cadus/incinerator/src/incinerator/incinerator.cpp

/*
 * SPDX-License-Identifier: GPL-3.0-or-later
 * This file is part of CADUS Incinerator, https://github.com/cadus/incinerator
 * Copyright (C) 2019-2020 Patrick Huesmann <info@patrick-huesmann.de>
 *
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
 * You should have received a copy of the GNU General Public License
 * along with this program.  If not, see <https://www.gnu.org/licenses/>.
 */

#include "incinerator.h"

#include <map>

#include "hw_config.h"
#include "util/sys_config.h"
#include "util/syslog.h"
#include "ui/screens/screen.h"

Incinerator::Incinerator()
: burnerMain("MAIN", IGNITION_MAIN, TEMP_MAIN_CS, VALVE_MAIN)
, burnerAft("AFT", IGNITION_AFT, TEMP_AFT_CS, VALVE_AFT)
, airPump(AIRPMP, PWM_CH_AIRPMP)
{
}

void Incinerator::init()
{
    burnerMain.init();
    burnerAft.init();
    airPump.init();
    reset();
}

void Incinerator::task()
{
    burnerMain.task();
    burnerAft.task();
    fsm();
}

Incinerator::mode Incinerator::getMode() const
{
    return _mode;
}

bool Incinerator::isCoolingDown() const
{
    return _mode == mode::coolDown
           || _mode == mode::abortCoolDown
           || _mode == mode::failureCoolDown;
}

bool Incinerator::isFinished() const
{
    return _mode == mode::finished
           || _mode == mode::aborted
           || _mode == mode::failed;
}

std::string Incinerator::getModeStr() const
{
    static const std::map<mode, std::string> lookupTbl {
        {idle, "Idle"},
        {startAft, "StartAft"},
        {waitAft, "WaitAft"},
        {startMain, "StartMain"},
        {waitMain, "WaitMain"},
        {burnActive, "BurnActive"},
        {coolDown, "CoolDown"},
        {finished, "Finished"},
        {failed, "Failed"}
    };
    auto it = lookupTbl.find(getMode());
    return it != lookupTbl.end() ? it->second : "N/A";
}

void Incinerator::start()
{
    _startFlag = true;
}

void Incinerator::abort()
{
    _abortFlag = true;
}

void Incinerator::reset()
{
    doReset();
    _mode = mode::idle;
}

void Incinerator::doReset()
{
    Screen::setProgress(0);
    burnerMain.reset();
    burnerAft.reset();
    airPump.off();
}

void Incinerator::doFail()
{
    doReset();
    _mode = mode::failureCoolDown;
}

void Incinerator::doAbort()
{
    syslog(LOG_INFO, "Burn process aborted by user");
    doReset();
    _mode = mode::abortCoolDown;
}

std::string Incinerator::fmt_minutes(uint32_t seconds) const
{
    char tmp[100];
    snprintf(tmp, sizeof(tmp), "%d:%02d", seconds / 60, seconds % 60);
    return std::string(tmp);
}


void Incinerator::fsm()
{
    float percent, temp;
    switch (_mode) {
    default:
    case mode::idle:
        if (!_startFlag) {
            break;
        }
        _startFlag = false;
        _abortFlag = false;
        _tempMax = nanf("");
        _mode = mode::startAft;
        // fall through
    case mode::startAft:
        syslog(LOG_INFO, "Starting afterburner");
        burnerAft.start();
        _mode = mode::waitAft;
        break;
    case mode::waitAft:
        if (_abortFlag) {
            doAbort();
            break;
        }
        if (burnerAft.getMode() == BurnChamber::mode::failed) {
            syslog(LOG_INFO, "Afterburner failed");
            doFail();
            break;
        }
        if (!burnerAft.isBurning()) {
            break;
        }
        _mode = mode::startMain;
        // fall through
    case mode::startMain:
        syslog(LOG_INFO, "Starting main burner");
        burnerMain.start();
        airPump.on();
        _mode = mode::waitMain;
        // fall through
    case mode::waitMain:
        if (_abortFlag) {
            doAbort();
            break;
        }
        if (burnerMain.getMode() == BurnChamber::mode::failed
            || burnerAft.getMode() == BurnChamber::mode::failed) {
            syslog(LOG_INFO, "Burner failed");
            doFail();
            break;
        }
        if (!burnerMain.isBurning()) {
            break;
        }
        _mode = mode::burnActive;
        _burn_seconds = sysconfig.get("burn_time") * 60;
        _burn_seconds_elapsed = 0;
        syslog(LOG_INFO, "Burning in progress");
        _timeout.set(1000);
        // fall through
    case mode::burnActive:
        if (_abortFlag) {
            doAbort();
            break;
        }
        if (burnerMain.getMode() == BurnChamber::mode::failed
            || burnerAft.getMode() == BurnChamber::mode::failed) {
            syslog(LOG_INFO, "Burner failed");
            doFail();
            break;
        }
        if (!_timeout.elapsed()) {
            break;
        }
        _burn_seconds_elapsed++;
        _timeout.set(1000);
        percent = (100.f * (float)_burn_seconds_elapsed) / (float)_burn_seconds;
        syslog(LOG_INFO, "Burning %s / %s (%d%%)",
                         fmt_minutes(_burn_seconds_elapsed).c_str(),
                         fmt_minutes(_burn_seconds).c_str(),
                         (int)percent);
        Screen::setProgress(percent);
        if (_burn_seconds_elapsed < _burn_seconds) {
            break;
        }
        doReset();
        _mode = mode::coolDown;
        syslog(LOG_INFO, "Burn finished, cooling down");
        // fall through
    case mode::coolDown:
    case mode::failureCoolDown:
    case mode::abortCoolDown:
        temp = max(burnerMain.thermocouple.get().external,
                   burnerAft.thermocouple.get().external);
        if (isnan(_tempMax)) {
            _tempMax = temp;
        }
        {
            const float coolTemp = sysconfig.get("cool_temp");
            float diff = temp - coolTemp;
            diff = diff > 0 ? diff : 0;
            percent = 100.f - (100.f * diff) / (_tempMax - coolTemp);
            syslog(LOG_INFO, "Cooling %dC -> %dC (%d%%)",
                            (int)temp,
                            (int)coolTemp,
                            (int)percent);
            Screen::setProgress(percent);
            if (temp > coolTemp) {
                break;
            }
            syslog(LOG_INFO, "Cool down finished");
            std::map<mode, mode> lookup {
                { mode::coolDown, mode::finished },
                { mode::abortCoolDown, mode::aborted },
                { mode::failureCoolDown, mode::failed }
            };
            _mode = lookup[_mode];
            doReset();
        }
        break;
    case mode::aborted:
    case mode::finished:
    case mode::failed:
        break;
    }
}

Incinerator incinerator;
