cadus/incinerator/src/display.cpp

#include "display.h"

#include <GxEPD2_BW.h>
#include <Fonts/FreeMonoBold9pt7b.h>

#include "hw_config.h"
#include "icons.h"
#include "thermocouple.h"
#include "debounced_encoder.h"
#include "incinerator.h"

extern void GxEPD2_busyWaitCallback();

#ifdef __AVR__
#define MAX_DISPLAY_BUFFER_SIZE 800
#define MAX_HEIGHT(EPD) (EPD::HEIGHT <= MAX_DISPLAY_BUFFER_SIZE / (EPD::WIDTH / 8) ? EPD::HEIGHT : MAX_DISPLAY_BUFFER_SIZE / (EPD::WIDTH / 8))
GxEPD2_BW<GxEPD2_420, MAX_HEIGHT(GxEPD2_420)> display(GxEPD2_420(EPD_CS, EPD_DC, EPD_RST, EPD_BUSY));
#else
GxEPD2_BW<GxEPD2_420, GxEPD2_420::HEIGHT> display(GxEPD2_420(EPD_CS, EPD_DC, EPD_RST, EPD_BUSY));
#endif

void display_init()
{
    display.init();
    display.setRotation(0);
    display.setFullWindow();
    display.fillScreen(GxEPD_WHITE);
    display.display(false); // full update
}

void display_redraw()
{
    static int cnt = 0;
    cnt++;

    display.setRotation(0);
    display.setFont(&FreeMonoBold9pt7b);
    display.setTextColor(GxEPD_BLACK);

    thermocouple_meas_t T = burner_main.getTemp();
    String str = "I:"
                 + String(T.internal, 2)
                 + ", E:"
                 + String(T.external, 2)
                 + ", e: "
                 + String(encoder_position())
                 + ", c: "
                 + String(cnt % 100);

    const uint8_t ep = max(min(encoder_position(), 25), 0);

    display.setPartialWindow(0, 0, display.width(), display.height());
    unsigned long start = micros();
    display.fillScreen(GxEPD_WHITE);
    display.setCursor(10, 15);
    display.print(str);
    for (uint8_t i = 0; i < 25; i++) {
        const uint8_t *icon = (ep > i) ? ICON_BOX_FILLED_DATA : ICON_BOX_CLEAR_DATA;
        display.drawBitmap(i * ICON_BOX_CLEAR_WIDTH, 20, icon, ICON_BOX_CLEAR_WIDTH, ICON_BOX_CLEAR_HEIGHT, GxEPD_BLACK);
    }
    display.display(true); // partial update
    unsigned long elapsed = micros() - start;
    Serial.print("time spent - w/o refresh: ");
    Serial.print(elapsed - 560000);
    Serial.println(" us");
    Serial.print("time spent - total: ");
    Serial.print(elapsed);
    Serial.println(" us");
}
